dimitri-rebrikov/tasmota_gasmeter/media/casing2.png

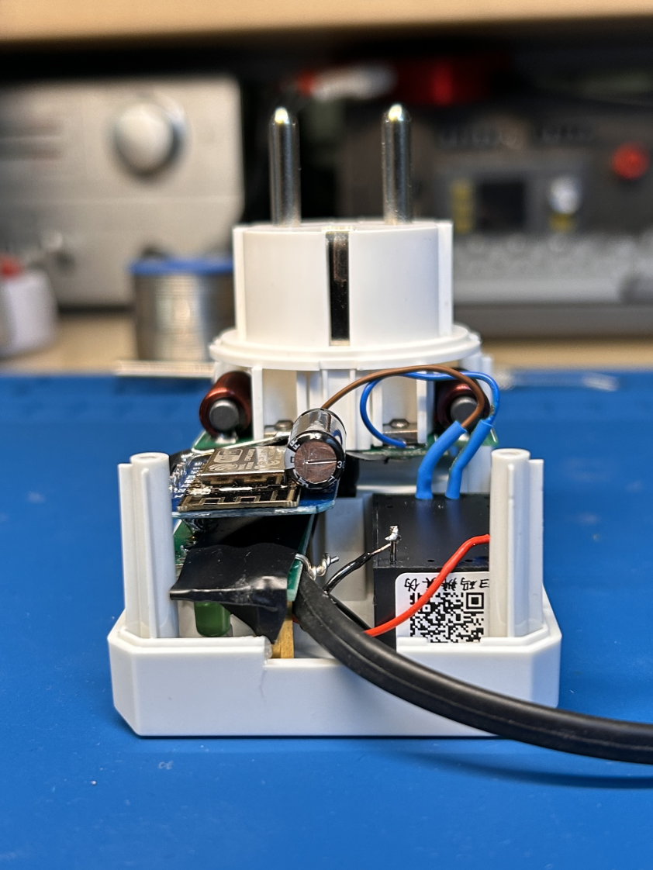
media/casing2.png
