dimitri-rebrikov/tasmota_gasmeter/media/casing4.png

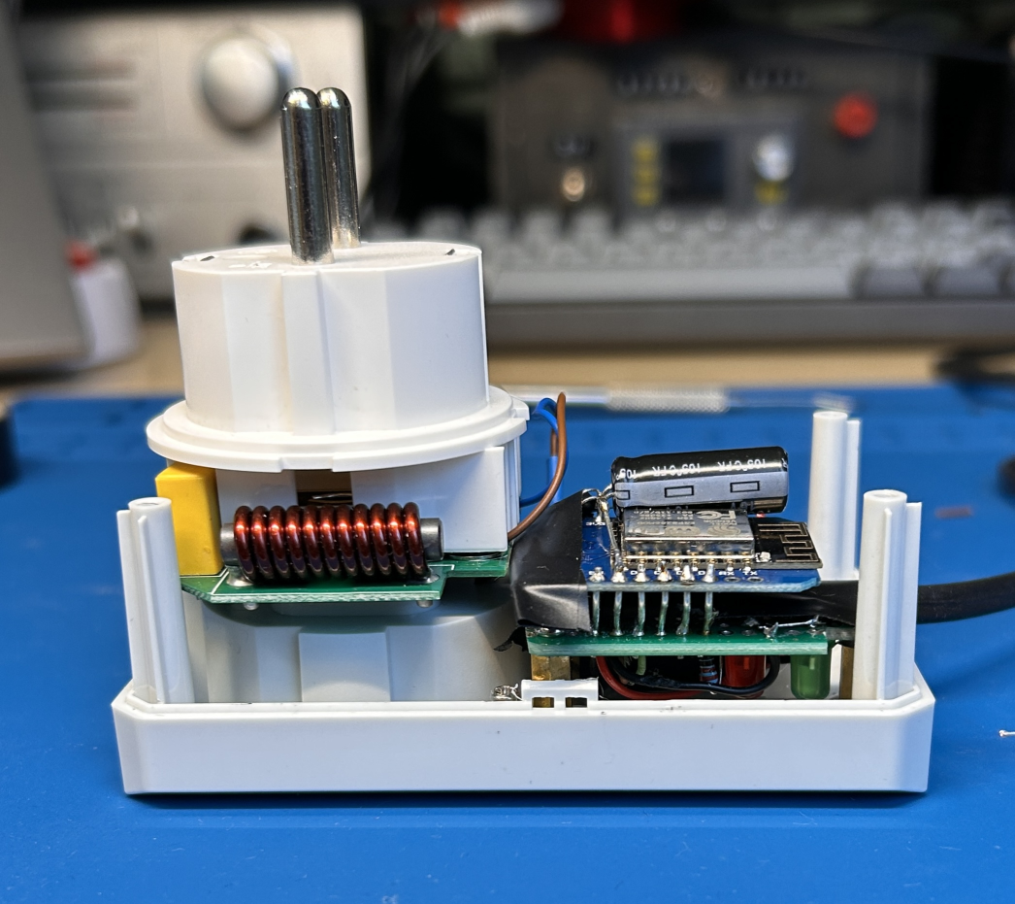
media/casing4.png
