dimitri-rebrikov/tasmota_gasmeter/media/casing7.png

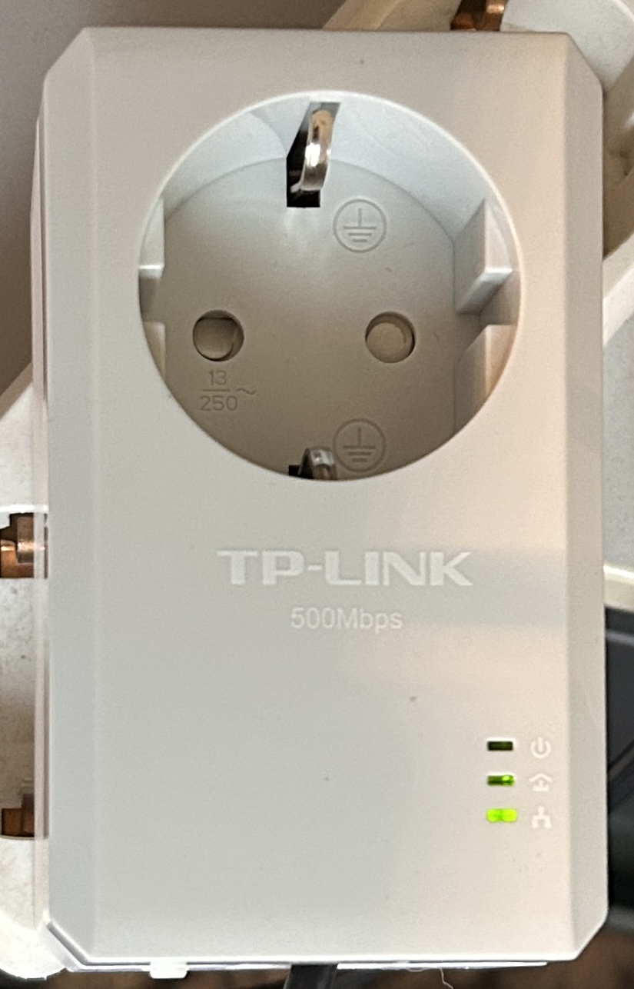
media/casing7.png
