dimitri-rebrikov/tasmota_gasmeter/media/circuit5.png

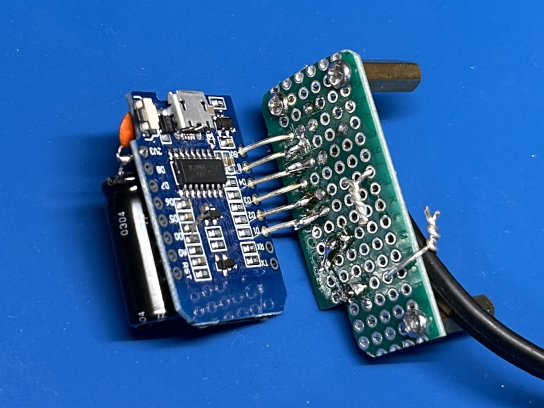
media/circuit5.png
